stefanschramm/z80pg2026/schematics/z80pg2026.kicad_sch

## KiCad design schematics/z80pg2026.kicad_sch (2026-06-01)

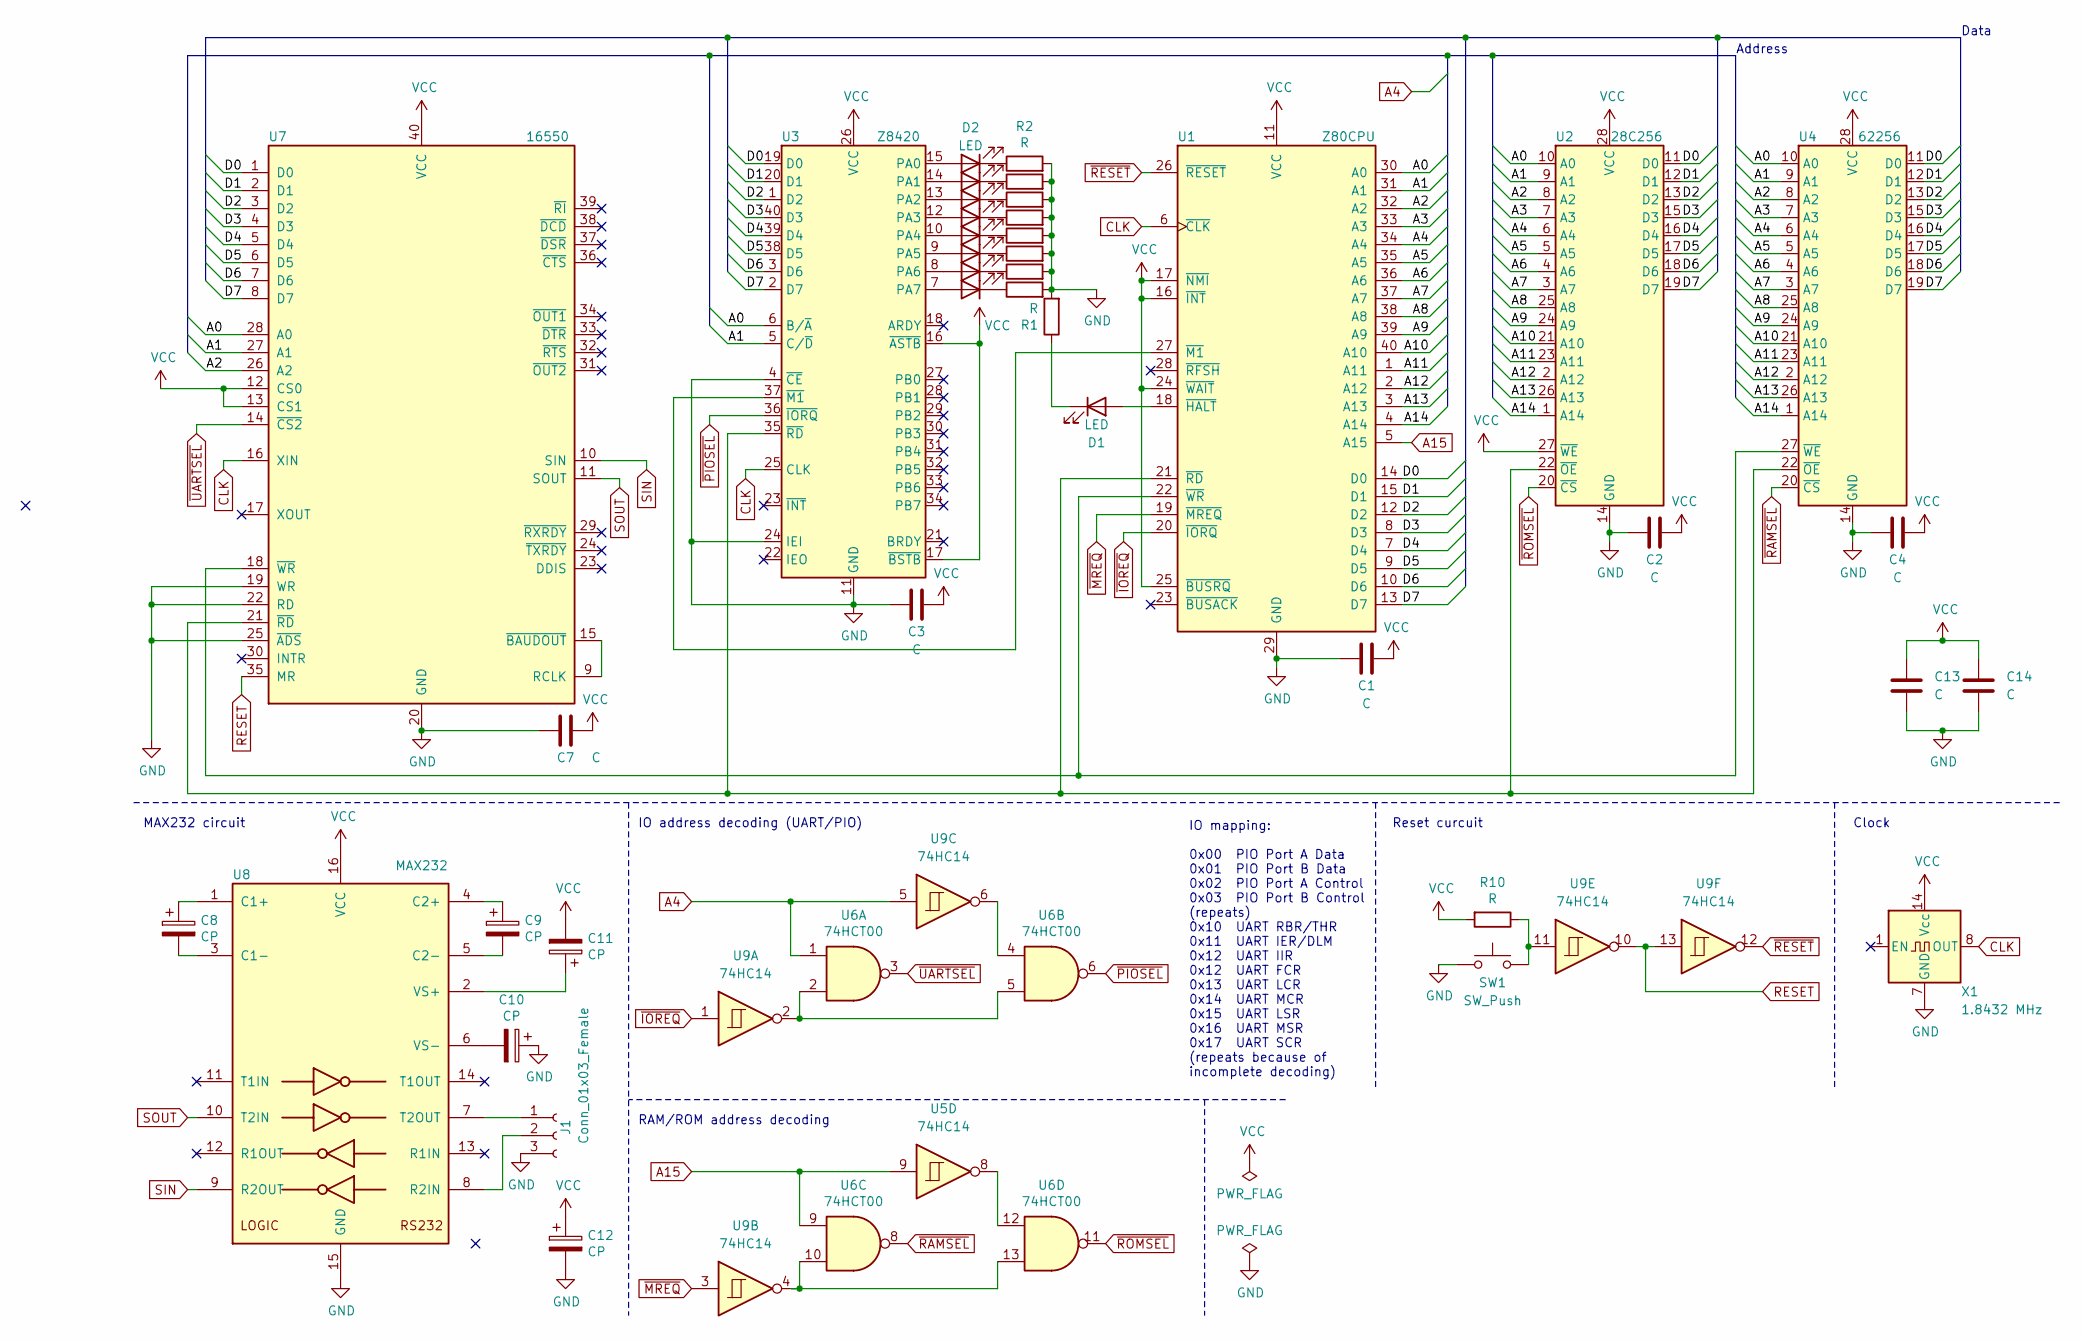
[picture p4: schematic z80pg2026.kicad_sch]

Parts:
C1, C2, C3, C4, C7, C13, C14: C
C8, C9, C10, C11, C12: CP
D1, D2, D3, D4, D5, D6, D7, D8, D9: LED
J1: Conn_01x03_Female
R1, R2, R3, R4, R5, R6, R7, R8, R9, R10: R
SW1: SW_Push
U1: Z80CPU
U2: 28C256
U3: Z8420; DIP-40_W15.24mm
U4: 62256
U5, U9: 74HC14
U6: 74HCT00
U7: 16550; DIP-40_W15.24mm
U8: MAX232
X1: 1.8432 MHz; Oscillator_DIP-14

Connections:
A0: U1.30 (A0), U2.10 (A0), U3.6 (B/~A), U4.10 (A0), U7.28 (A0)
A1: U1.31 (A1), U2.9 (A1), U3.5 (C/~D), U4.9 (A1), U7.27 (A1)
A2: U1.32 (A2), U2.8 (A2), U4.8 (A2), U7.26 (A2)
A3: U1.33 (A3), U2.7 (A3), U4.7 (A3)
A4: U1.34 (A4), U2.6 (A4), U4.6 (A4), U6.1, U9.5
A5: U1.35 (A5), U2.5 (A5), U4.5 (A5)
A6: U1.36 (A6), U2.4 (A6), U4.4 (A6)
A7: U1.37 (A7), U2.3 (A7), U4.3 (A7)
A8: U1.38 (A8), U2.25 (A8), U4.25 (A8)
A9: U1.39 (A9), U2.24 (A9), U4.24 (A9)
A10: U1.40 (A10), U2.21 (A10), U4.21 (A10)
A11: U1.1 (A11), U2.23 (A11), U4.23 (A11)
A12: U1.2 (A12), U2.2 (A12), U4.2 (A12)
A13: U1.3 (A13), U2.26 (A13), U4.26 (A13)
A14: U1.4 (A14), U2.1 (A14), U4.1 (A14)
A15: U1.5 (A15), U5.9, U6.9
CLK: U1.6 (~CLK), U3.25 (CLK), U7.16 (XIN), X1.8 (OUT)
D0: U1.14 (D0), U2.11 (D0), U3.19 (D0), U4.11 (D0), U7.1 (D0)
D1: U1.15 (D1), U2.12 (D1), U3.20 (D1), U4.12 (D1), U7.2 (D1)
D2: U1.12 (D2), U2.13 (D2), U3.1 (D2), U4.13 (D2), U7.3 (D2)
D3: U1.8 (D3), U2.15 (D3), U3.40 (D3), U4.15 (D3), U7.4 (D3)
D4: U1.7 (D4), U2.16 (D4), U3.39 (D4), U4.16 (D4), U7.5 (D4)
D5: U1.9 (D5), U2.17 (D5), U3.38 (D5), U4.17 (D5), U7.6 (D5)
D6: U1.10 (D6), U2.18 (D6), U3.3 (D6), U4.18 (D6), U7.7 (D6)
D7: U1.13 (D7), U2.19 (D7), U3.2 (D7), U4.19 (D7), U7.8 (D7)
GND: C1.1, C2.1, C3.1, C4.1, C7.1, C10.1, C12.2, C13.2, C14.2, J1.3, R1.2, R2.2, R3.2, R4.2, R5.2, R6.2, R7.2, R8.2, R9.2, SW1.1, U1.29 (GND), U2.14 (GND), U3.4 (~CE), U3.11 (GND), U3.24 (IEI), U4.14 (GND), U7.19 (WR), U7.20 (GND), U7.22 (RD), U7.25 (~ADS), U8.15 (GND), X1.7 (GND)
unnamed: C8.1, U8.1 (C1+)
unnamed: C8.2, U8.3 (C1-)
unnamed: C9.1, U8.4 (C2+)
unnamed: C9.2, U8.5 (C2-)
unnamed: C10.2, U8.6 (VS-)
unnamed: C11.1, U8.2 (VS+)
unnamed: D1.1 (K), R1.1
unnamed: D1.2 (A), U1.18 (~HALT)
unnamed: D2.1 (K), R2.1
unnamed: D2.2 (A), U3.15 (PA0)
unnamed: D3.1 (K), R3.1
unnamed: D3.2 (A), U3.14 (PA1)
unnamed: D4.1 (K), R4.1
unnamed: D4.2 (A), U3.13 (PA2)
unnamed: D5.1 (K), R5.1
unnamed: D5.2 (A), U3.12 (PA3)
unnamed: D6.1 (K), R6.1
unnamed: D6.2 (A), U3.10 (PA4)
unnamed: D7.1 (K), R7.1
unnamed: D7.2 (A), U3.9 (PA5)
unnamed: D8.1 (K), R8.1
unnamed: D8.2 (A), U3.8 (PA6)
unnamed: D9.1 (K), R9.1
unnamed: D9.2 (A), U3.7 (PA7)
unnamed: J1.1, U8.7 (T2OUT)
unnamed: J1.2, U8.8 (R2IN)
unnamed: R10.1, SW1.2, U9.11
unnamed: U1.21 (~RD), U2.22 (~OE), U3.35 (~RD), U4.22 (~OE), U7.21 (~RD)
unnamed: U1.22 (~WR), U4.27 (~WE), U7.18 (~WR)
unnamed: U1.27 (~M1), U3.37 (~M1)
unnamed: U5.8, U6.12
unnamed: U6.2, U6.5, U9.2
unnamed: U6.4, U9.6
unnamed: U6.10, U6.13, U9.4
unnamed: U7.9 (RCLK), U7.15 (~BAUDOUT)
RESET: U7.35 (MR), U9.10, U9.13
SIN: U7.10 (SIN), U8.9 (R2OUT)
SOUT: U7.11 (SOUT), U8.10 (T2IN)
VCC: C1.2, C2.2, C3.2, C4.2, C7.2, C11.2, C12.1, C13.1, C14.1, R10.2, U1.11 (VCC), U1.16 (~INT), U1.17 (~NMI), U1.24 (~WAIT), U1.25 (~BUSRQ), U2.27 (~WE), U2.28 (VCC), U3.16 (~ASTB), U3.17 (~BSTB), U3.26 (VCC), U4.28 (VCC), U7.12 (CS0), U7.13 (CS1), U7.40 (VCC), U8.16 (VCC), X1.14 (Vcc)
~IOREQ: U1.20 (~IORQ), U9.1
~MREQ: U1.19 (~MREQ), U9.3
~PIOSEL: U3.36 (~IORQ), U6.6
~RAMSEL: U4.20 (~CS), U6.8
~RESET: U1.26 (~RESET), U9.12
~ROMSEL: U2.20 (~CS), U6.11
~UARTSEL: U6.3, U7.14 (~CS2)

Notes on the sheet:
IO address decoding (UART/PIO)
Data
MAX232 circuit
IO mapping: 0x00 PIO Port A Data 0x01 PIO Port B Data 0x02 PIO Port A Control 0x03 PIO Port B Control (repeats) 0x10 UART RBR/THR 0x11 UART IER/DLM 0x12 UART IIR 0x12 UART FCR 0x13 UART LCR 0x14 UART MCR 0x15 UART LSR 0x16 UART MSR 0x17 UART SCR (repeats because of incomplete decoding)
RAM/ROM address decoding
Address
Clock
Reset curcuit
